whoim2/arduremote/IMG_20200811_004400_096.jpg

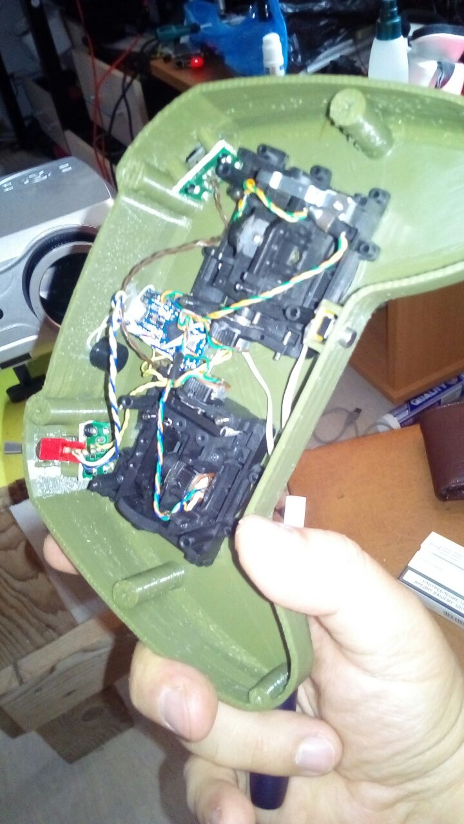
IMG_20200811_004400_096.jpg
